onitake/pcb-workshop/output/nametag-B.SilkS.pdf

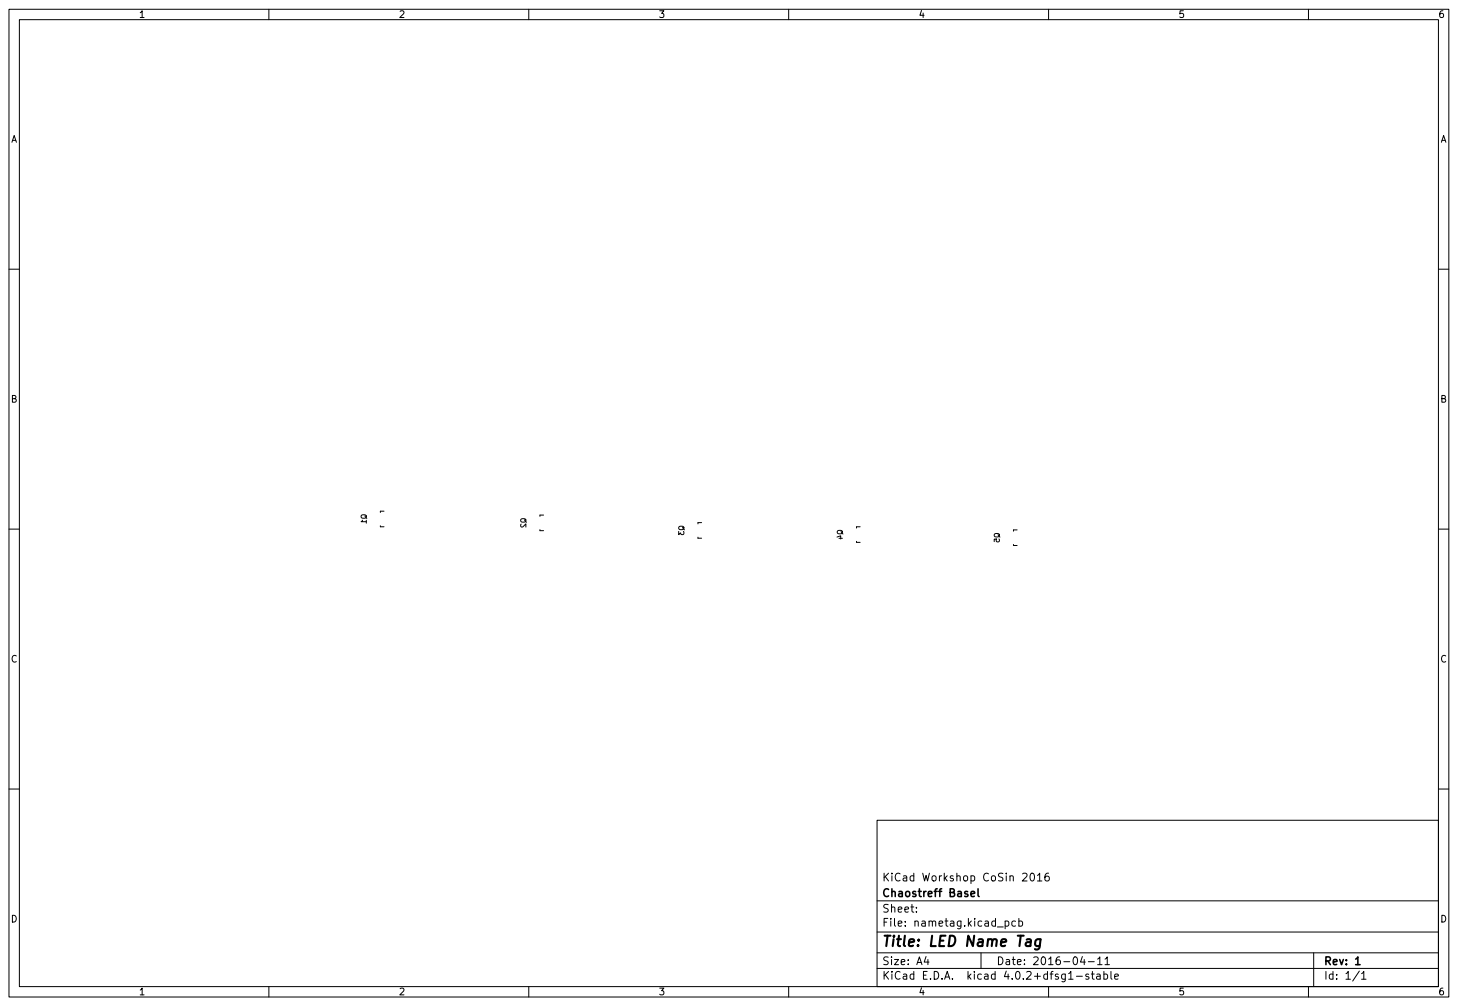
[picture p9: page 1]

Id: 1/1 Title: LED Name Tag
