onitake/pcb-workshop/output/nametag_smd-B.Cu.pdf

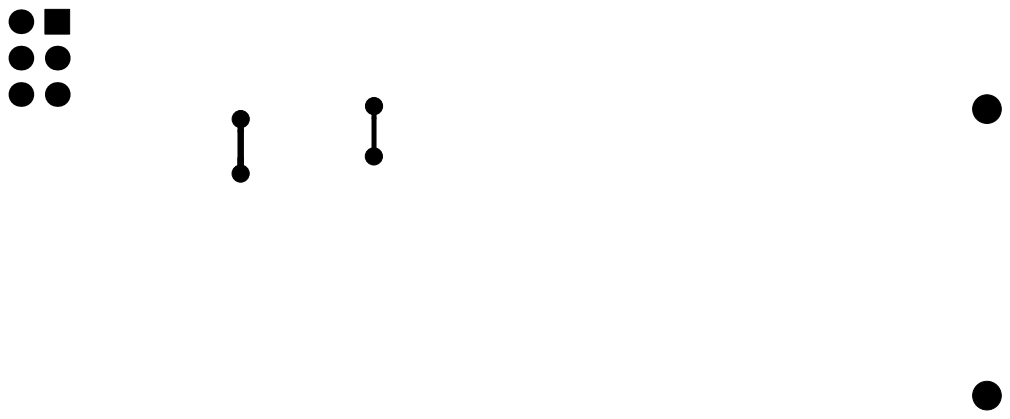
[picture p10: page 1]

File: nametag_smd.kicad_pcb Sheet: Ruum42 KiCad Workhop CoSin 2016

Id: 1/1 Title: LED Name Tag SMD
